teezzan/sweech/images/img1.jpg

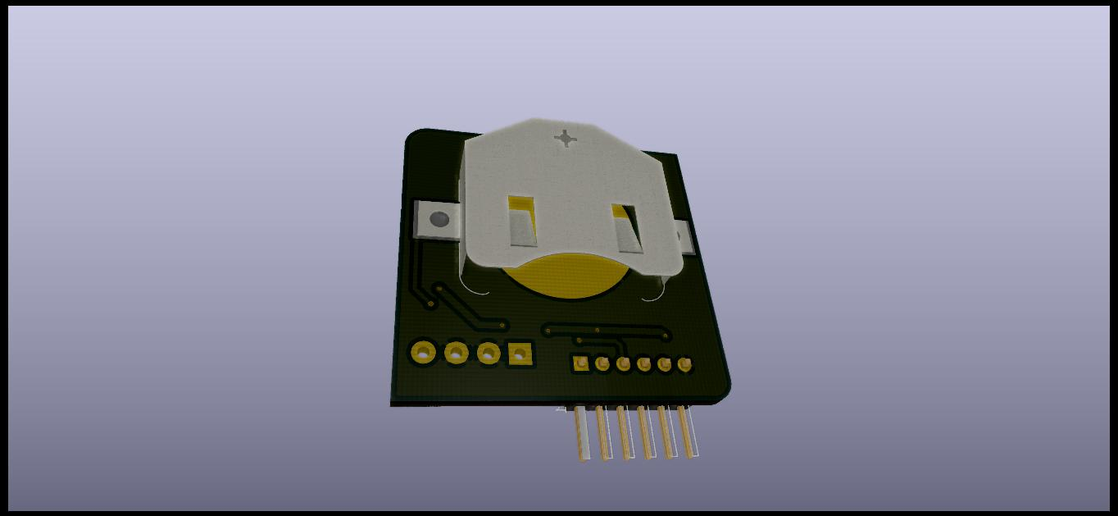
images/img1.jpg
