teezzan/sweech/images/img2.png

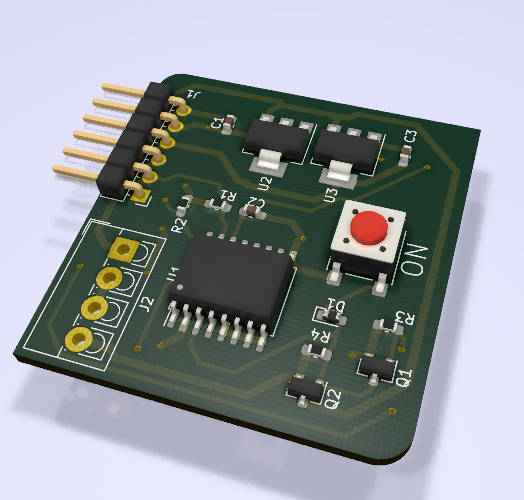
images/img2.png
