teezzan/sweech/images/img3.png

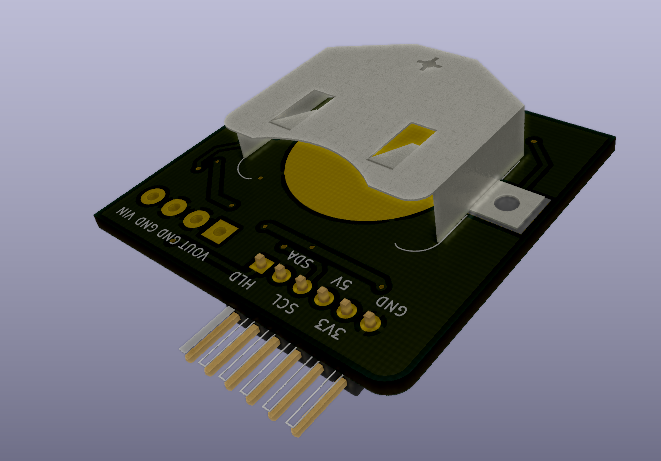
images/img3.png
